CuriosityGym/idIoTware-Shield/datasheets/HXD Buzzer.jpg

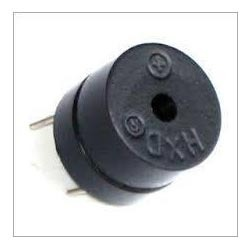
datasheets/HXD Buzzer.jpg
