CuriosityGym/idIoTware-Shield/datasheets/LDR.jpg

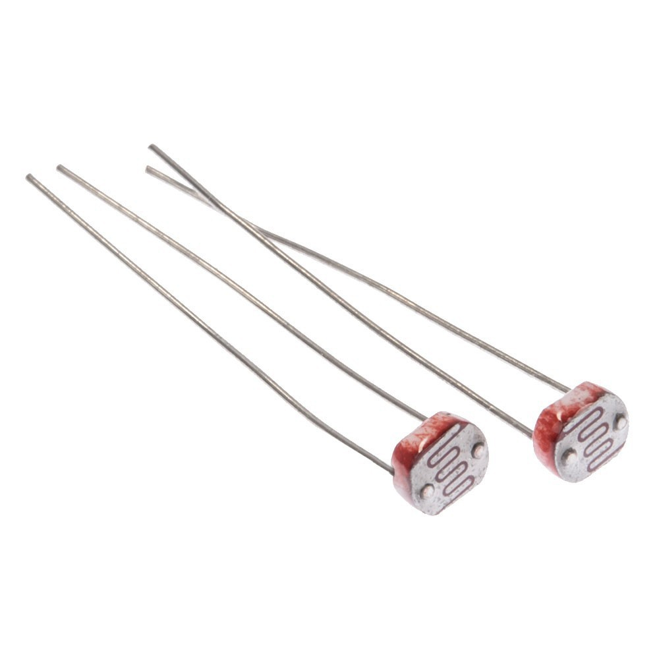
datasheets/LDR.jpg
