CuriosityGym/idIoTware-Shield/datasheets/MicroSwitch.jpg

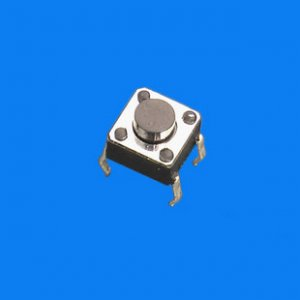
datasheets/MicroSwitch.jpg
