CuriosityGym/idIoTware-Shield/images/1.png

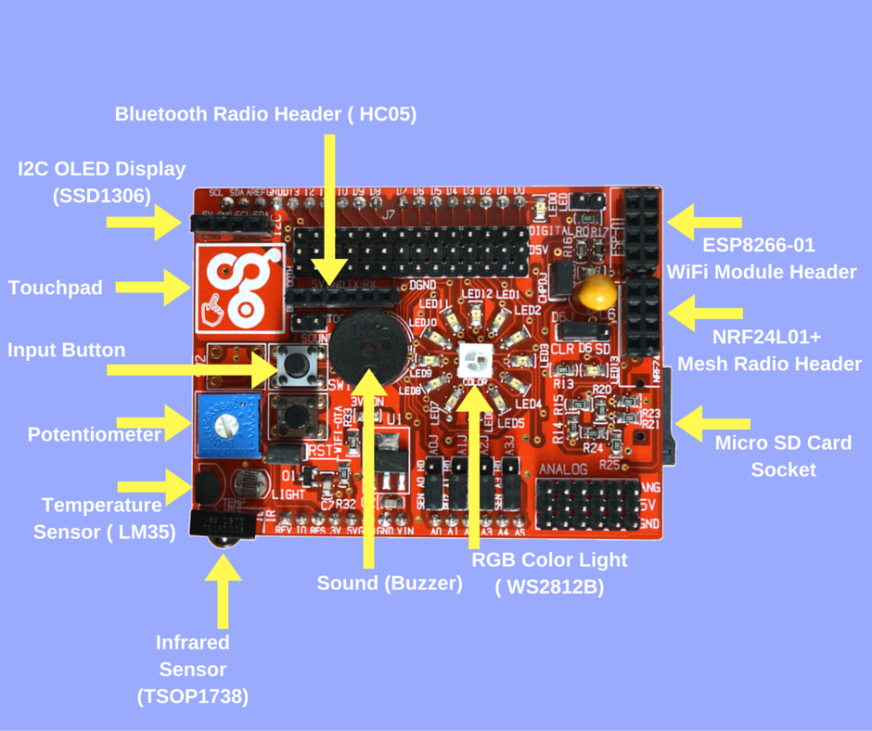
images/1.png
