CuriosityGym/idIoTware-Shield/images/2.png

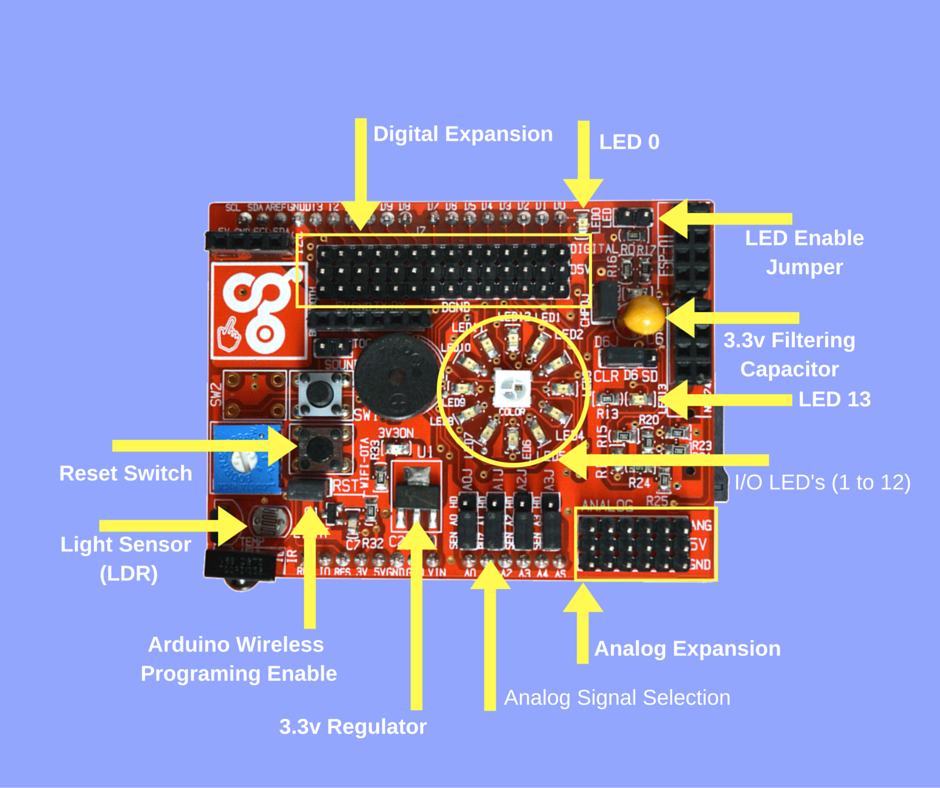
images/2.png
