CuriosityGym/idIoTware-Shield/images/idIoTware Shield On Arduino with NRF Radio.JPG

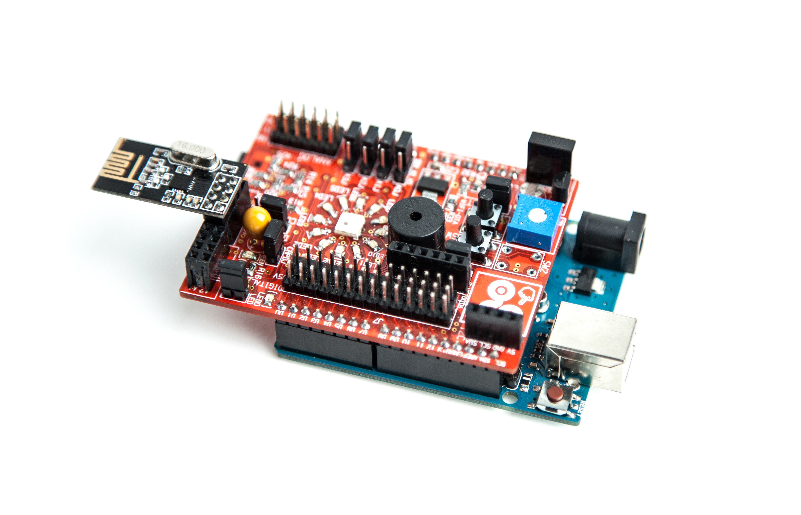
images/idIoTware Shield On Arduino with NRF Radio.JPG
