CuriosityGym/idIoTware-Shield/Lesson-Plans/Expert/TwitterSentiment/ESPlink settings.jpg

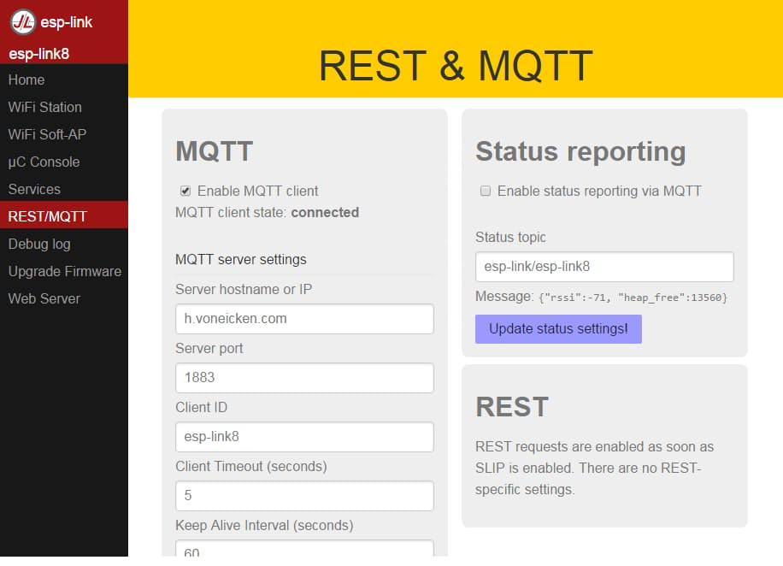
Lesson-Plans/Expert/TwitterSentiment/ESPlink settings.jpg
