CuriosityGym/idIoTware-Shield/Lesson-Plans/Expert/TwitterSentiment/Function Node'.jpg

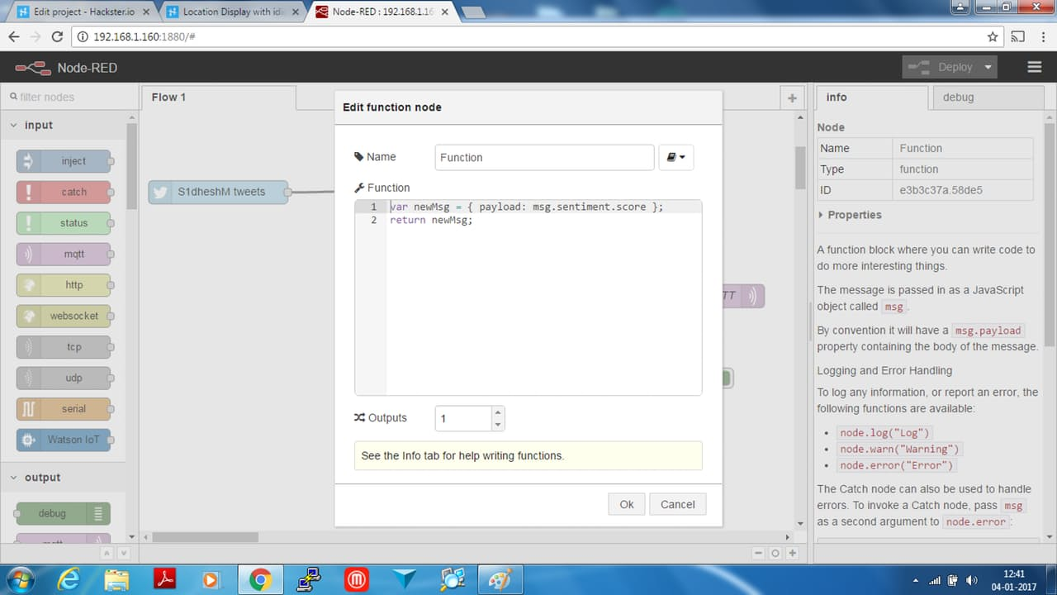
Lesson-Plans/Expert/TwitterSentiment/Function Node'.jpg
