CuriosityGym/idIoTware-Shield/Lesson-Plans/Expert/TwitterSentiment/MQTT Node.jpg

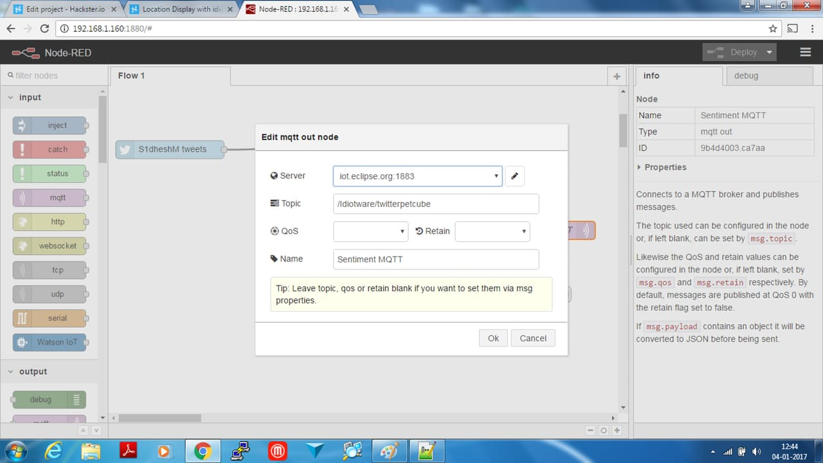
Lesson-Plans/Expert/TwitterSentiment/MQTT Node.jpg
