CuriosityGym/idIoTware-Shield/Lesson-Plans/Expert/TwitterSentiment/Node Red Twitter.jpg

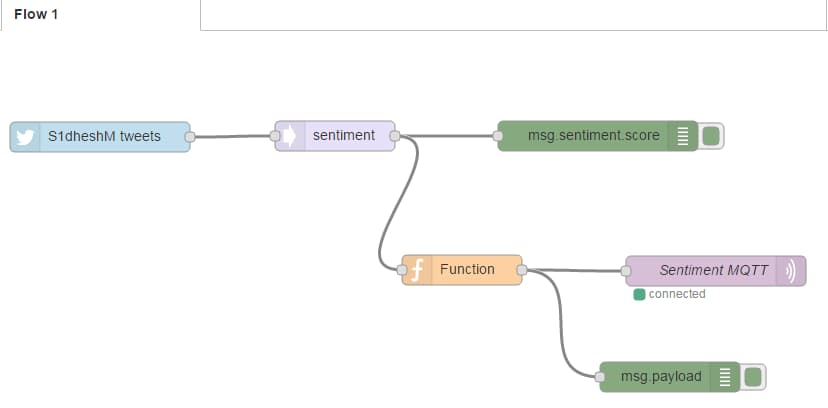
Lesson-Plans/Expert/TwitterSentiment/Node Red Twitter.jpg
