CuriosityGym/idIoTware-Shield/Lesson-Plans/Intermediate/weatherStation/icons.h

#define icon_width 40
#define icon_height 40
static const unsigned char clear_sky[] PROGMEM = {
  0x00, 0x00, 0x00, 0x00, 0x00, 0x00, 0x00, 0x00, 0x00, 0x00, 0x00, 0x00, 
  0x00, 0x00, 0x00, 0x00, 0x00, 0x00, 0x00, 0x00, 0x00, 0x40, 0x00, 0x00, 
  0x00, 0x00, 0x40, 0x00, 0x04, 0x00, 0x00, 0xC0, 0x00, 0x06, 0x00, 0x00, 
  0xC0, 0x01, 0x06, 0x00, 0x00, 0xC0, 0x01, 0x07, 0x00, 0x00, 0x80, 0x83, 
  0x03, 0x00, 0x00, 0x80, 0xC3, 0x03, 0x00, 0x00, 0x80, 0x01, 0x03, 0x00, 
  0x00, 0x00, 0x3C, 0x00, 0x00, 0xE0, 0x01, 0xFF, 0x01, 0x00, 0xC0, 0xCF, 
  0xFF, 0x83, 0x05, 0x00, 0xCF, 0xFF, 0xF3, 0x07, 0x00, 0xE6, 0xFF, 0xE7, 
  0x01, 0x00, 0xE4, 0xFF, 0x67, 0x00, 0x00, 0xF0, 0xFF, 0x2F, 0x00, 0x00, 
  0xF0, 0xFF, 0x0F, 0x00, 0x00, 0xF0, 0xFF, 0x0F, 0x00, 0x00, 0xF0, 0xFF, 
  0x0F, 0x00, 0x00, 0xE6, 0xFF, 0x2F, 0x00, 0x80, 0xEF, 0xFF, 0x67, 0x00, 
  0xC0, 0xCF, 0xFF, 0xF7, 0x00, 0xB0, 0xC1, 0xFF, 0xF3, 0x03, 0x00, 0x80, 
  0xFF, 0x80, 0x07, 0x00, 0x00, 0x7E, 0x00, 0x00, 0x00, 0xC0, 0x00, 0x01, 
  0x00, 0x00, 0xC0, 0xE3, 0x01, 0x00, 0x00, 0xC0, 0xC1, 0x01, 0x00, 0x00, 
  0xE0, 0x80, 0x03, 0x00, 0x00, 0x60, 0x80, 0x01, 0x00, 0x00, 0x60, 0x00, 
  0x03, 0x00, 0x00, 0x20, 0x00, 0x02, 0x00, 0x00, 0x00, 0x00, 0x02, 0x00, 
  0x00, 0x00, 0x00, 0x00, 0x00, 0x00, 0x00, 0x00, 0x00, 0x00, 0x00, 0x00, 
  0x00, 0x00, 0x00, 0x00, 0x00, 0x00, 0x00, 0x00, 
  };   


static const unsigned char few_clouds[] PROGMEM= {
  0x00, 0x80, 0x01, 0x00, 0x00, 0x00, 0x80, 0x03, 0x00, 0x00, 0x00, 0x80, 
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
  0x0F, 0x00, 0x00, 0x00, 0x00, 0x00, 0x00, 0x00, 0x00, 0xFE, 0x0F, 0x00, 
  0x00, 0x00, 0x00, 0x00, 0x00, 0x00, 0x00, 0xF8, 0x07, 0x00, 0x00, 0x00, 
  0x00, 0x00, 0x00, 0x00, 0x00, 0xF0, 0x01, 0x00, 0x00, 0x00, 0x00, 0x00, 
  0x00, 0x00,  };   
